KFrydryk/GCloud-Soil-Moisture-Sensor/ciotc_config_template.h

/******************************************************************************
 * Copyright 2018 Google
 * Licensed under the Apache License, Version 2.0 (the "License");
 * you may not use this file except in compliance with the License.
 * You may obtain a copy of the License at
 *
 *    http://www.apache.org/licenses/LICENSE-2.0
 *
 * Unless required by applicable law or agreed to in writing, software
 * distributed under the License is distributed on an "AS IS" BASIS,
 * WITHOUT WARRANTIES OR CONDITIONS OF ANY KIND, either express or implied.
 * See the License for the specific language governing permissions and
 * limitations under the License.
 *****************************************************************************/
// This file contains your configuration used to connect to Cloud IoT Core

// WIFI
const char* ssid = "SSID";
const char* password = "PASSWORD";

// Cloud iot details.
const char* project_id = "project-id";
const char* location = "us-central1";
const char* registry_id = "my-registry";
const char* device_id = "my-device";

// Configuration for NTP
const char* ntp_primary = "pool.ntp.org";
const char* ntp_secondary = "time.nist.gov";

// To get the private key run (where private-key.pem is the ec private key
// used to create the certificate uploaded to google cloud iot):
// openssl ec -in <private-key.pem> -noout -text
// and copy priv: part.
// The key length should be exactly the same as the key length bellow (32 pairs
// of hex digits). If it's bigger and it starts with "00:" delete the "00:". If
// it's smaller add "00:" to the start. If it's too big or too small something
// is probably wrong with your key.
const char* private_key_str =
    "5a:2e:06:b5:c1:f2:9c:b3:77:b2:89:f5:29:29:93:"
    "07:fd:ed:22:0d:03:2b:a6:b1:b6:04:0b:d5:9b:49:"
    "7d:ca";

// Time (seconds) to expire token += 20 minutes for drift
const int jwt_exp_secs = 3600; // Maximum 24H (3600*24)

// Certificates for SSL on the LTS server
const char* primary_ca = "-----BEGIN CERTIFICATE-----\n"
    "MIIBxTCCAWugAwIBAgINAfD3nVndblD3QnNxUDAKBggqhkjOPQQDAjBEMQswCQYD\n"
    "VQQGEwJVUzEiMCAGA1UEChMZR29vZ2xlIFRydXN0IFNlcnZpY2VzIExMQzERMA8G\n"
    "A1UEAxMIR1RTIExUU1IwHhcNMTgxMTAxMDAwMDQyWhcNNDIxMTAxMDAwMDQyWjBE\n"
    "MQswCQYDVQQGEwJVUzEiMCAGA1UEChMZR29vZ2xlIFRydXN0IFNlcnZpY2VzIExM\n"
    "QzERMA8GA1UEAxMIR1RTIExUU1IwWTATBgcqhkjOPQIBBggqhkjOPQMBBwNCAATN\n"
    "8YyO2u+yCQoZdwAkUNv5c3dokfULfrA6QJgFV2XMuENtQZIG5HUOS6jFn8f0ySlV\n"
    "eORCxqFyjDJyRn86d+Iko0IwQDAOBgNVHQ8BAf8EBAMCAYYwDwYDVR0TAQH/BAUw\n"
    "AwEB/zAdBgNVHQ4EFgQUPv7/zFLrvzQ+PfNA0OQlsV+4u1IwCgYIKoZIzj0EAwID\n"
    "SAAwRQIhAPKuf/VtBHqGw3TUwUIq7TfaExp3bH7bjCBmVXJupT9FAiBr0SmCtsuk\n"
    "miGgpajjf/gFigGM34F9021bCWs1MbL0SA==\n"
    "-----END CERTIFICATE-----\n";

const char* backup_ca = "-----BEGIN CERTIFICATE-----\n"
    "MIIB4TCCAYegAwIBAgIRKjikHJYKBN5CsiilC+g0mAIwCgYIKoZIzj0EAwIwUDEk\n"
    "MCIGA1UECxMbR2xvYmFsU2lnbiBFQ0MgUm9vdCBDQSAtIFI0MRMwEQYDVQQKEwpH\n"
    "bG9iYWxTaWduMRMwEQYDVQQDEwpHbG9iYWxTaWduMB4XDTEyMTExMzAwMDAwMFoX\n"
    "DTM4MDExOTAzMTQwN1owUDEkMCIGA1UECxMbR2xvYmFsU2lnbiBFQ0MgUm9vdCBD\n"
    "QSAtIFI0MRMwEQYDVQQKEwpHbG9iYWxTaWduMRMwEQYDVQQDEwpHbG9iYWxTaWdu\n"
    "MFkwEwYHKoZIzj0CAQYIKoZIzj0DAQcDQgAEuMZ5049sJQ6fLjkZHAOkrprlOQcJ\n"
    "FspjsbmG+IpXwVfOQvpzofdlQv8ewQCybnMO/8ch5RikqtlxP6jUuc6MHaNCMEAw\n"
    "DgYDVR0PAQH/BAQDAgEGMA8GA1UdEwEB/wQFMAMBAf8wHQYDVR0OBBYEFFSwe61F\n"
    "uOJAf/sKbvu+M8k8o4TVMAoGCCqGSM49BAMCA0gAMEUCIQDckqGgE6bPA7DmxCGX\n"
    "kPoUVy0D7O48027KqGx2vKLeuwIgJ6iFJzWbVsaj8kfSt24bAgAXqmemFZHe+pTs\n"
    "ewv4n4Q=\n"
    "-----END CERTIFICATE-----\n";

// In case we ever need extra topics
const int ex_num_topics = 0;
const char* ex_topics[ex_num_topics];
//const int ex_num_topics = 1;
//const char* ex_topics[ex_num_topics] = {
//  "/devices/my-device/tbd/#"
//};
